dentex/arduino_macro_keyboard/images/connections_[incomplete].png

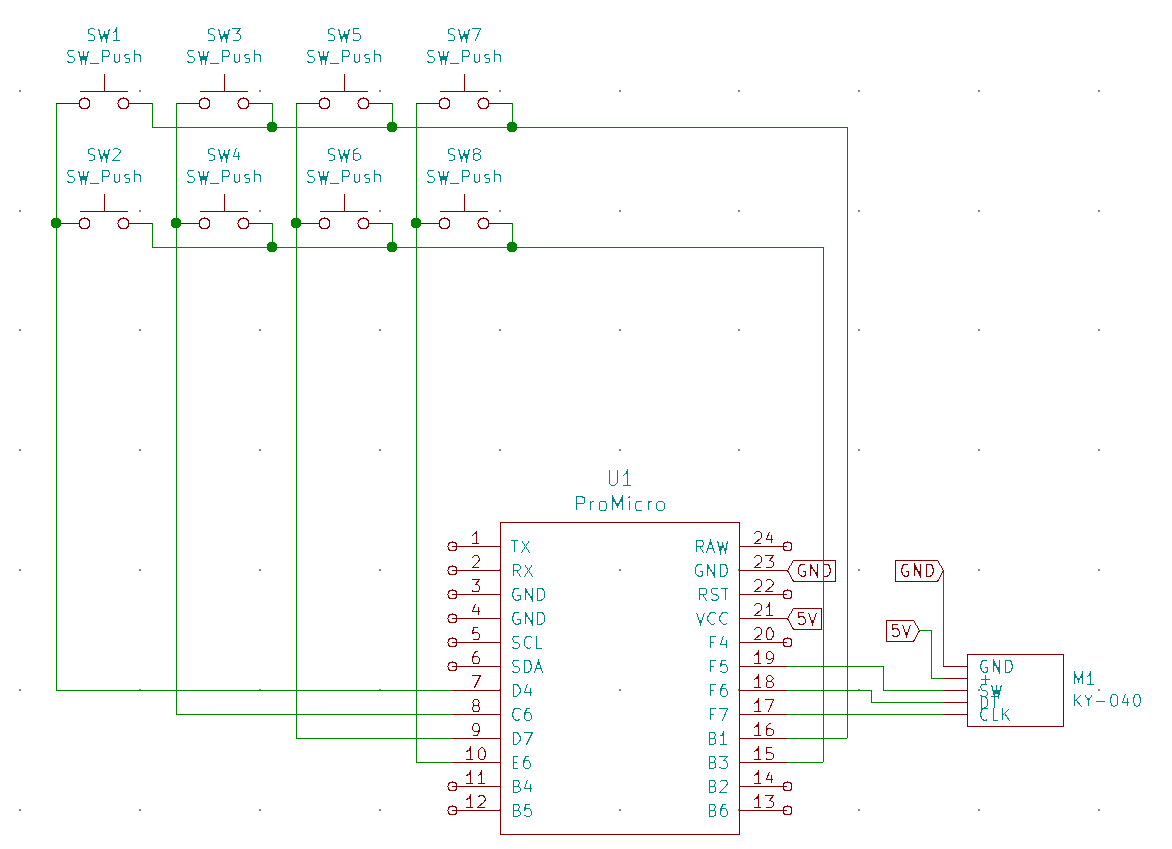
images/connections_[incomplete].png
