dentex/arduino_macro_keyboard/images/IMG_20210111.jpg

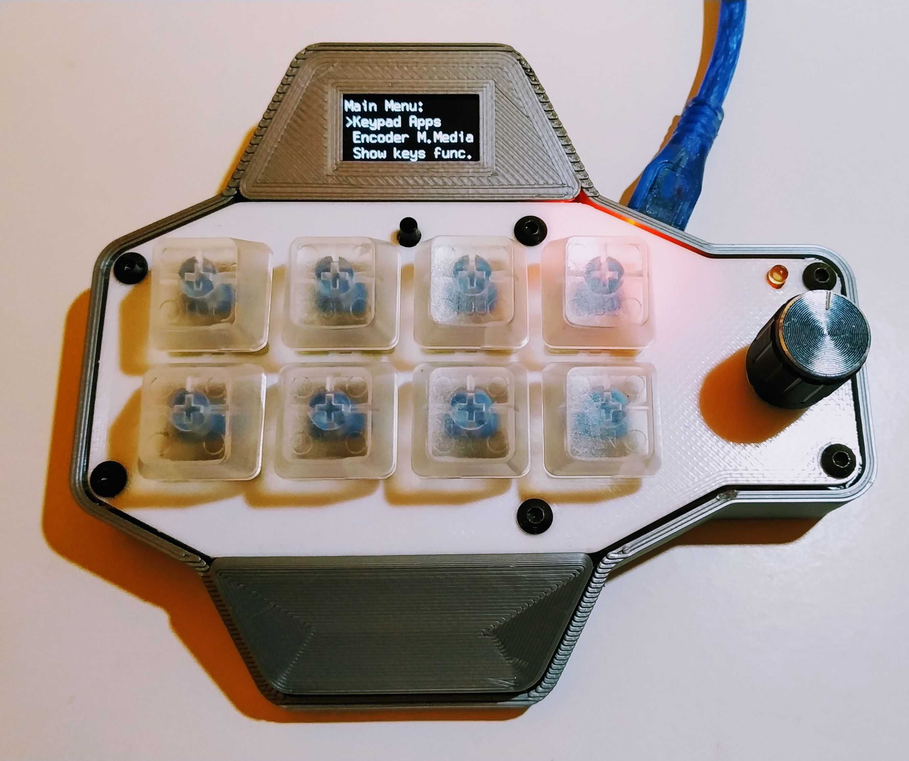
images/IMG_20210111.jpg
