dentex/arduino_macro_keyboard/images/IMG_20220331_155554.jpg

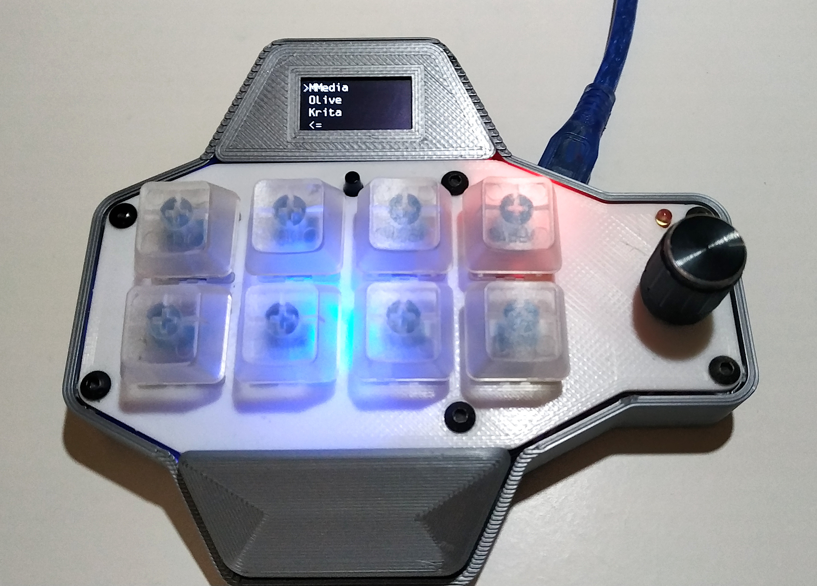
images/IMG_20220331_155554.jpg
