dentex/arduino_macro_keyboard/images/o1.png

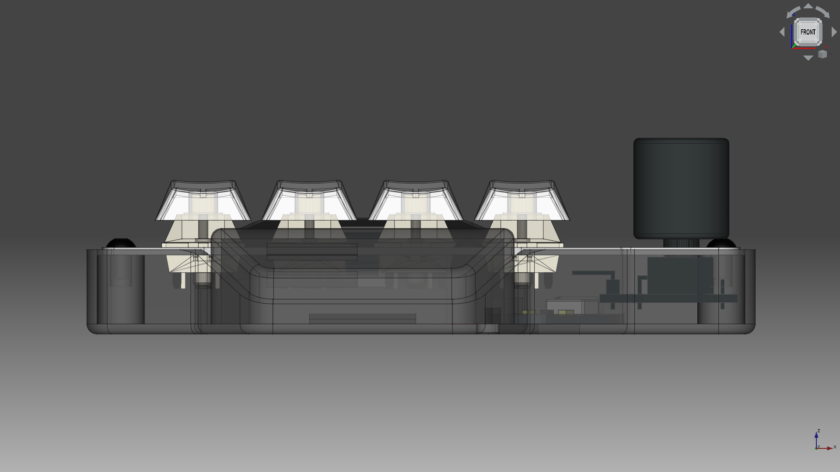
images/o1.png
