dentex/arduino_macro_keyboard/images/o2.png

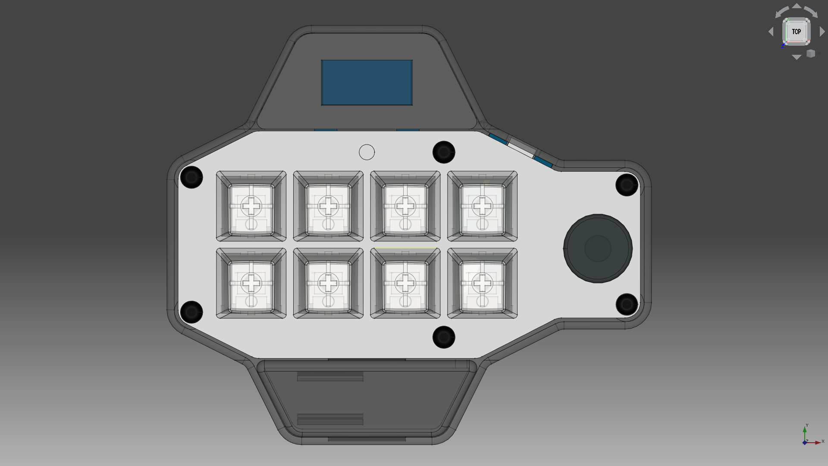
images/o2.png
