dentex/arduino_macro_keyboard/images/p1.png

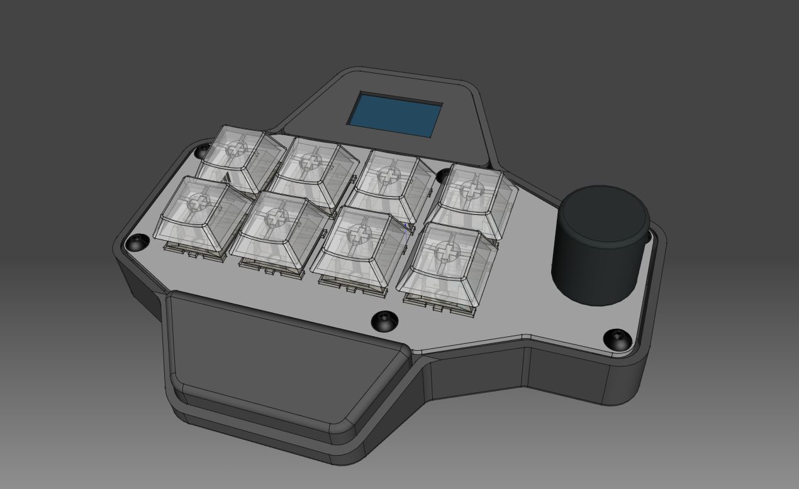
images/p1.png
