dentex/arduino_macro_keyboard/images/p2.png

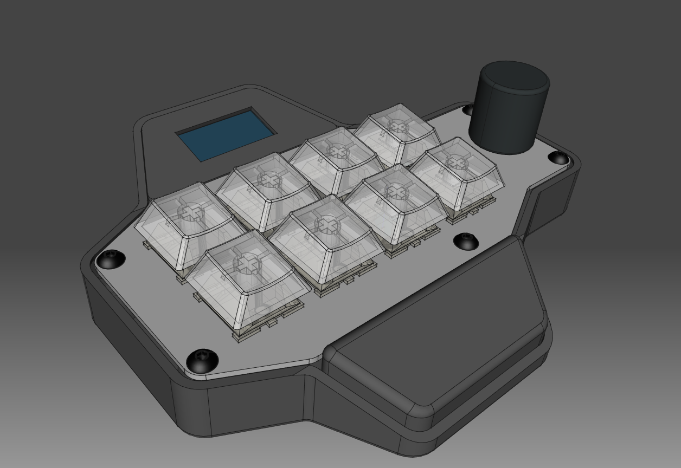
images/p2.png
