dentex/arduino_macro_keyboard/images/photo_2022-04-01_11-26-36.jpg

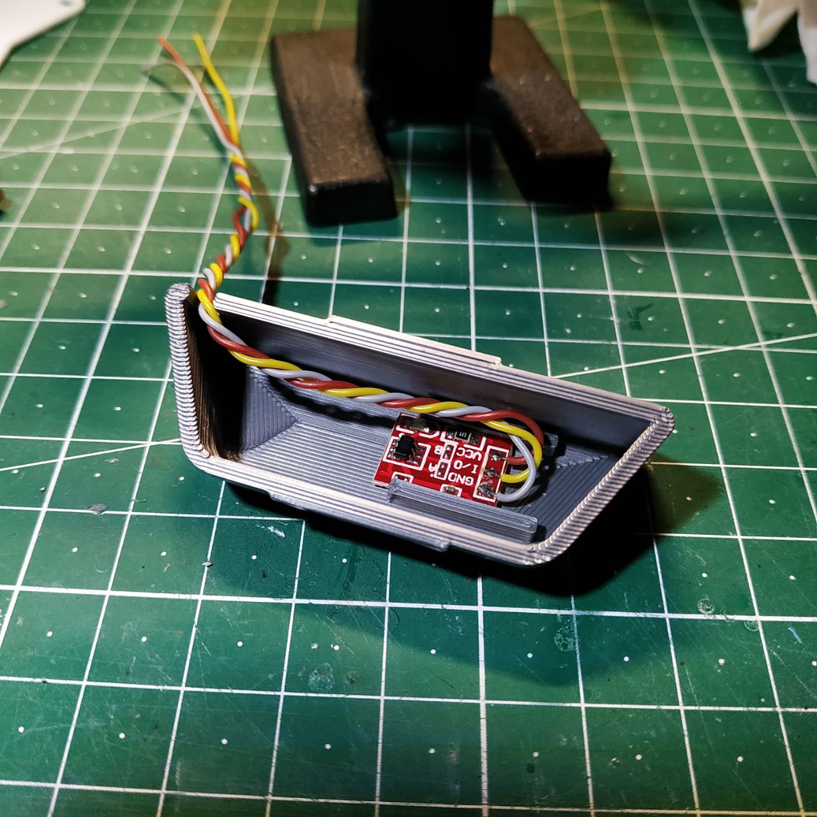
images/photo_2022-04-01_11-26-36.jpg
