dentex/arduino_macro_keyboard/images/photo_2022-04-01_11-27-35.jpg

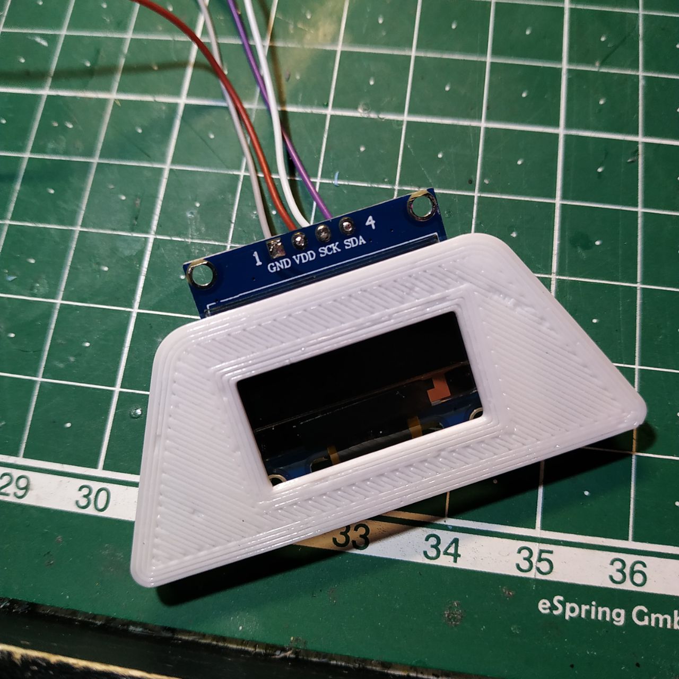
images/photo_2022-04-01_11-27-35.jpg
